ale1800/YULC/3D&Dimensions/yulc_dimensions.png

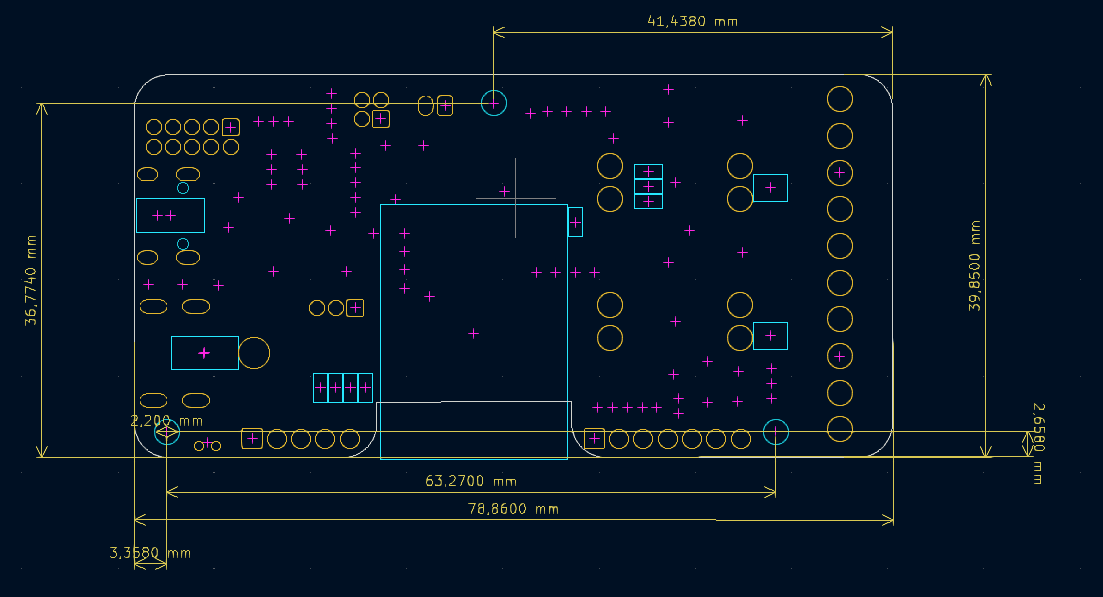
3D&Dimensions/yulc_dimensions.png
