ale1800/YULC/images/enclosure/case-2.jpg

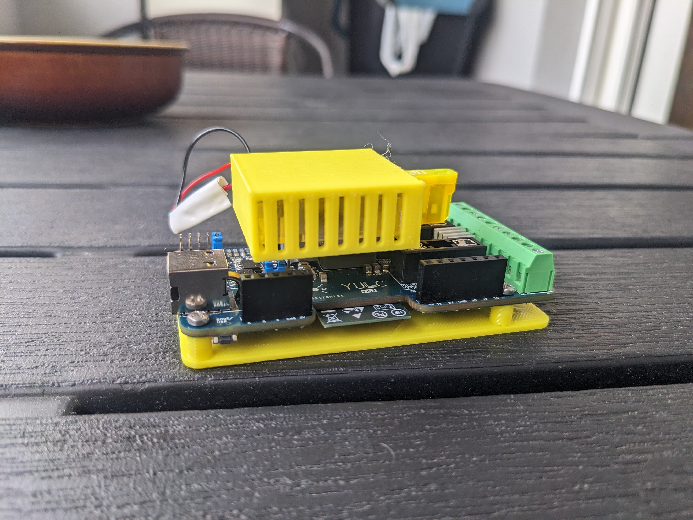
images/enclosure/case-2.jpg
