ale1800/YULC/images/enclosure/case-3.jpg

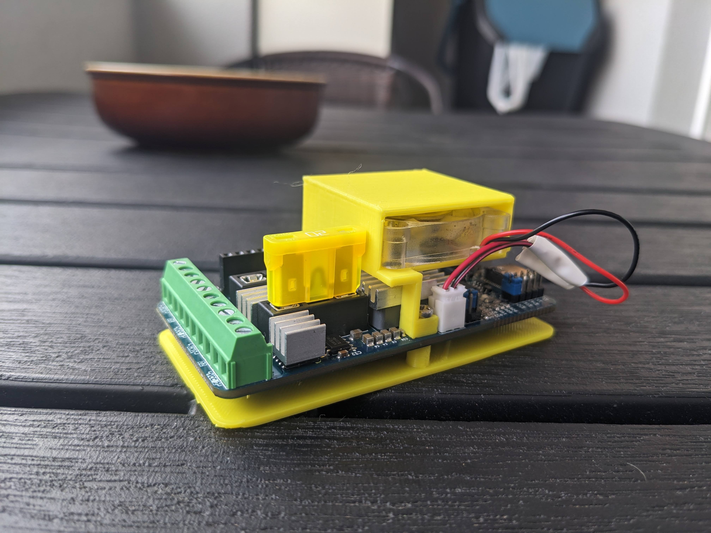
images/enclosure/case-3.jpg
