ale1800/YULC/images/enclosure/case-5.jpg

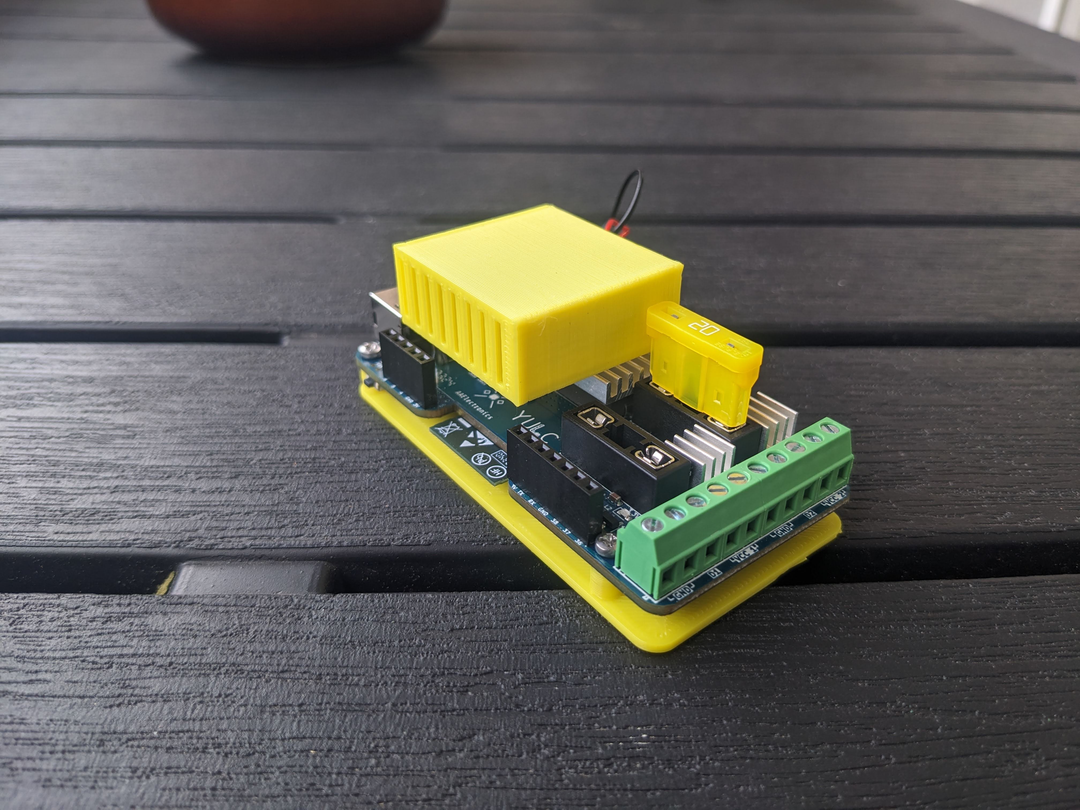
images/enclosure/case-5.jpg
