ale1800/YULC/images/real_use/side.jpg

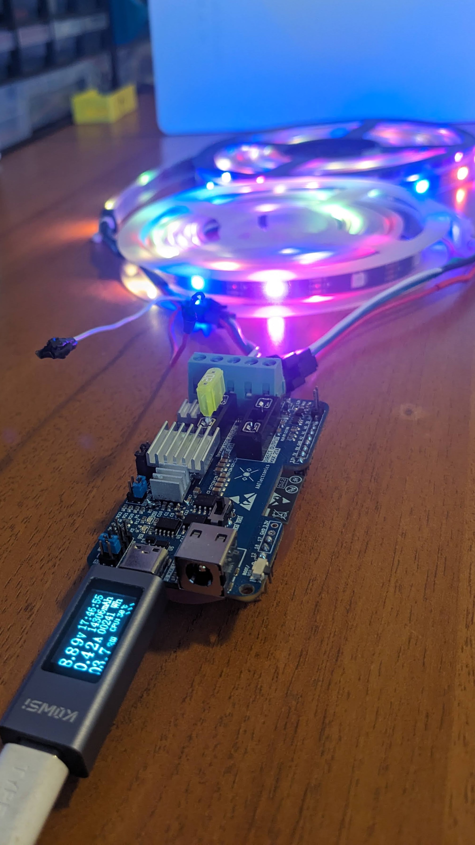
images/real_use/side.jpg
