ale1800/YULC/images/real_use/top_yellow.jpg

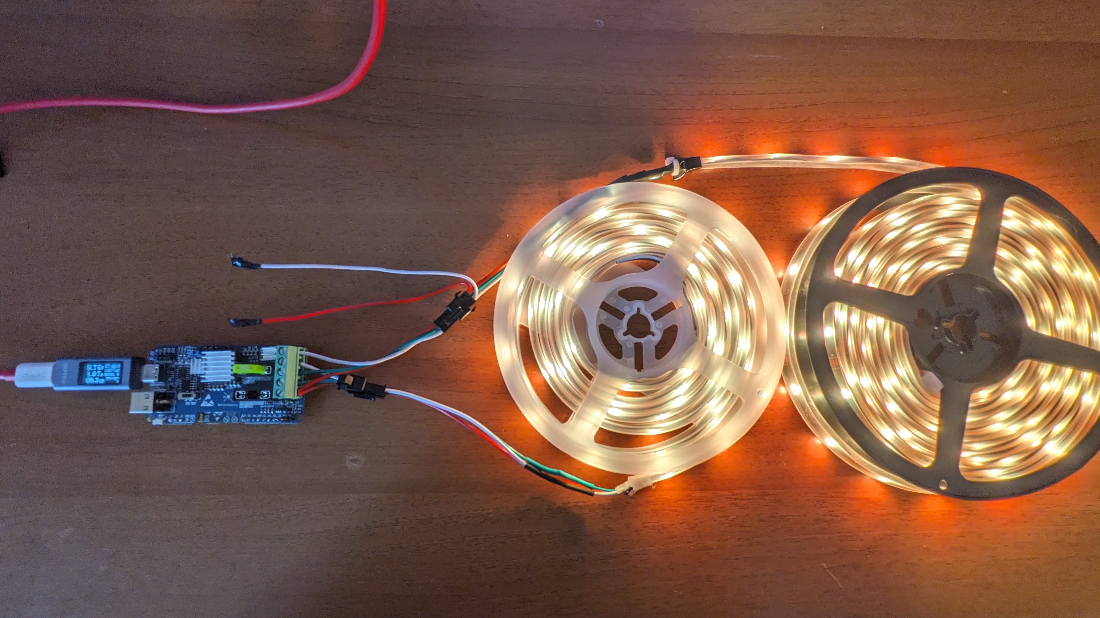
images/real_use/top_yellow.jpg
