ale1800/YULC/images/real_use/top_yulc.jpg

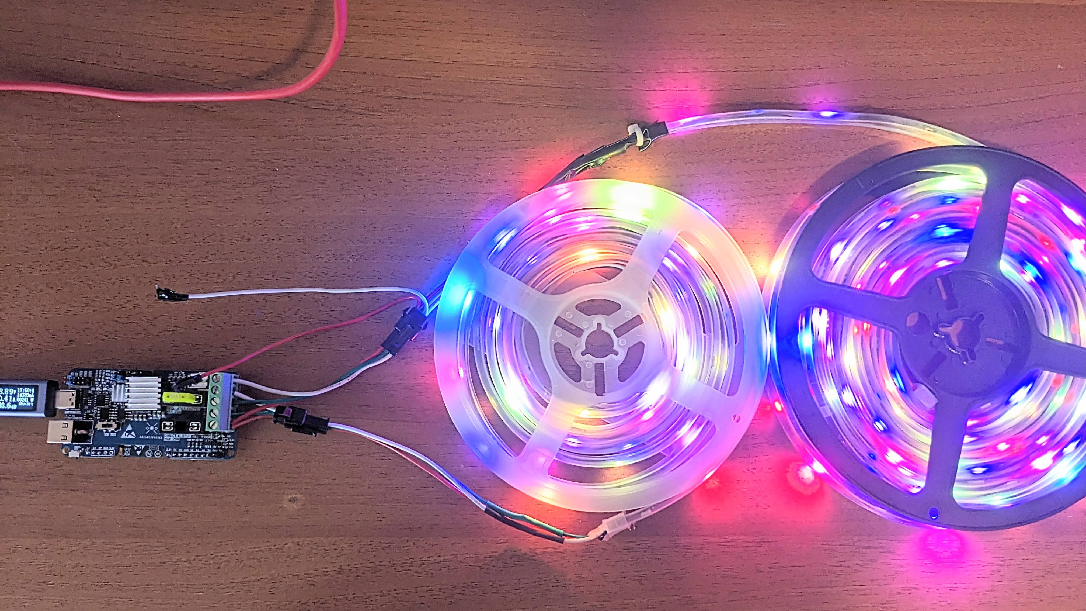
images/real_use/top_yulc.jpg
