ale1800/YULC/images/v2.1/angle-2.jpg

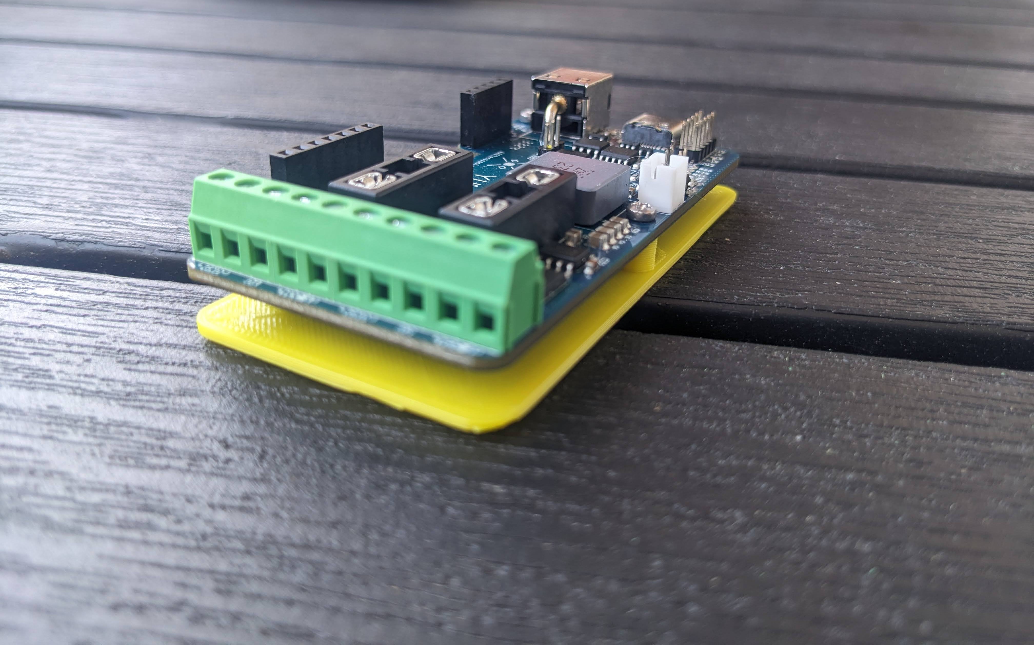
images/v2.1/angle-2.jpg
