ale1800/YULC/images/v2.1/angled.jpg

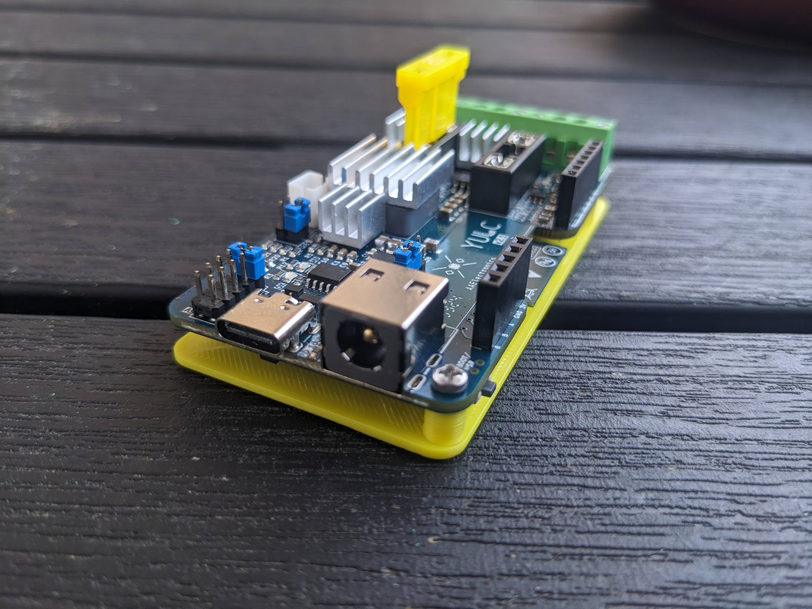
images/v2.1/angled.jpg
