ale1800/YULC/images/v2.1/base_screw.jpg

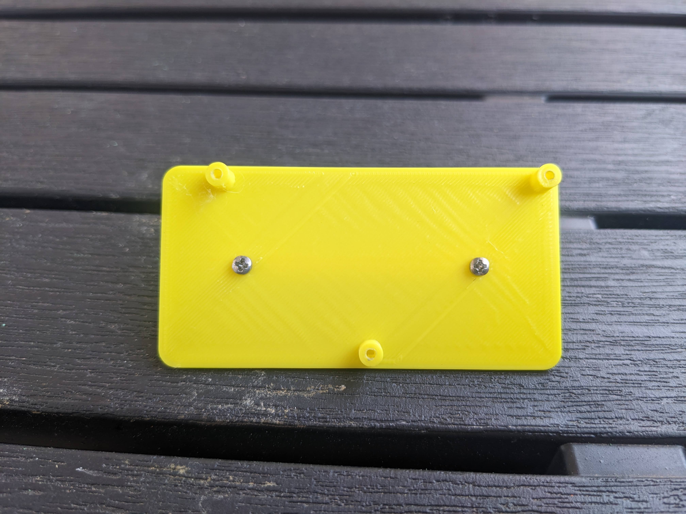
images/v2.1/base_screw.jpg
