ale1800/YULC/images/v2.1/DIN-side.jpg

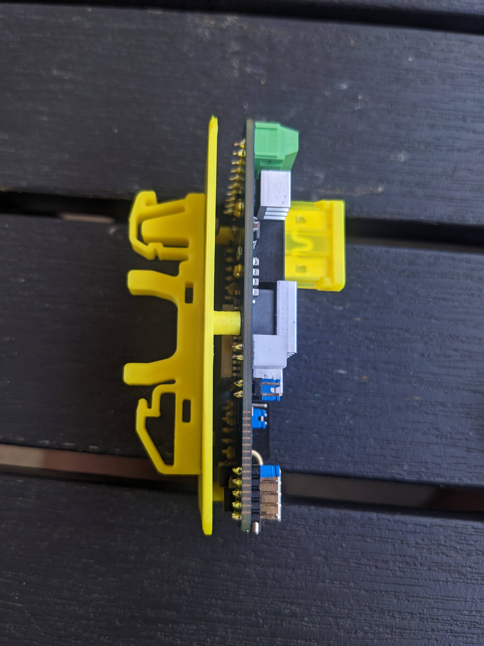
images/v2.1/DIN-side.jpg
