ale1800/YULC/images/v2.1/front_v2.1.jpg

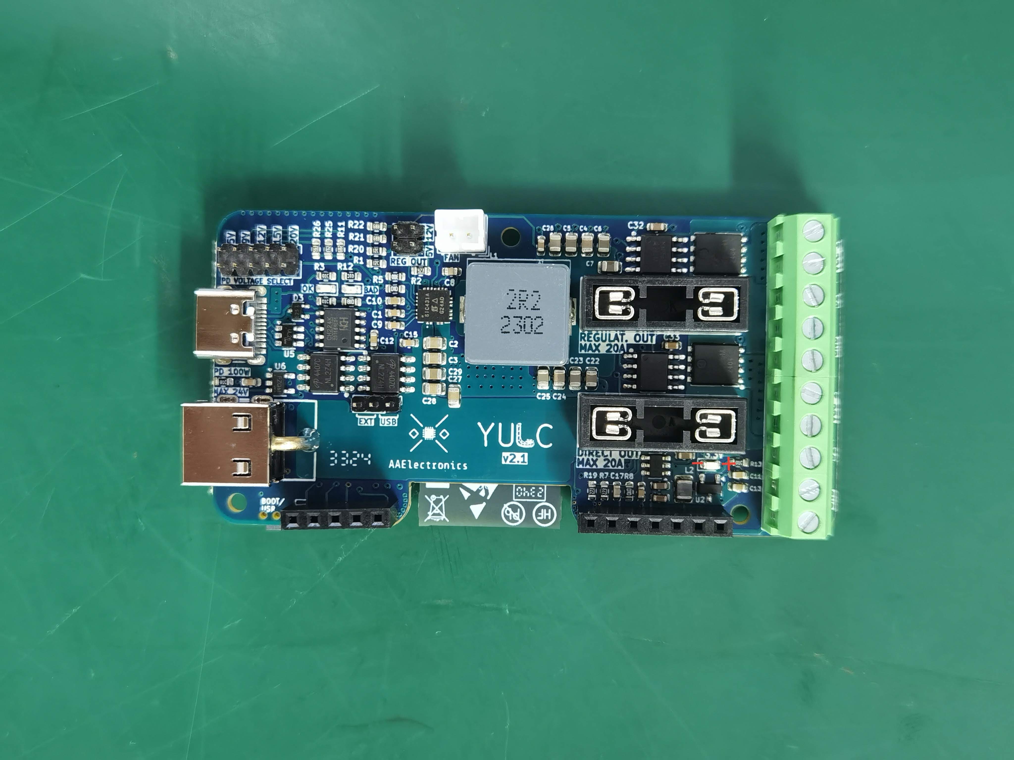
images/v2.1/front_v2.1.jpg
