ale1800/YULC/images/v2.1/side-1.jpg

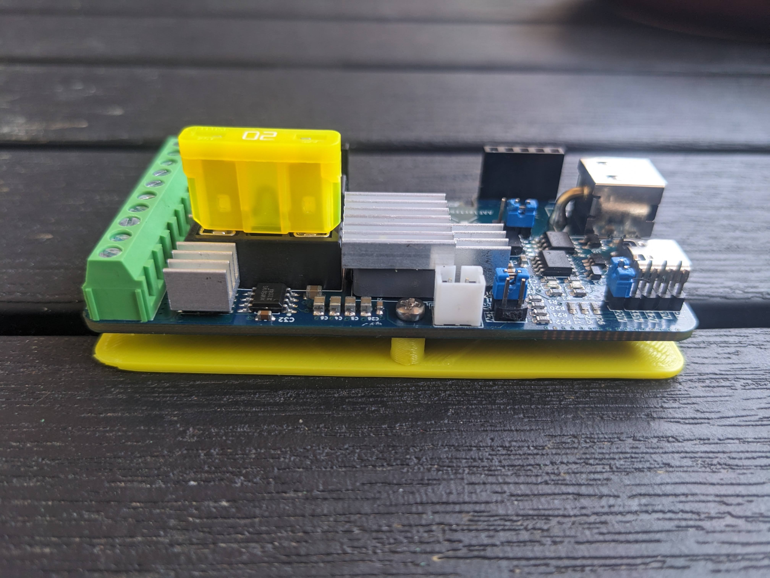
images/v2.1/side-1.jpg
