ale1800/YULC/images/v2.1/side-2.jpg

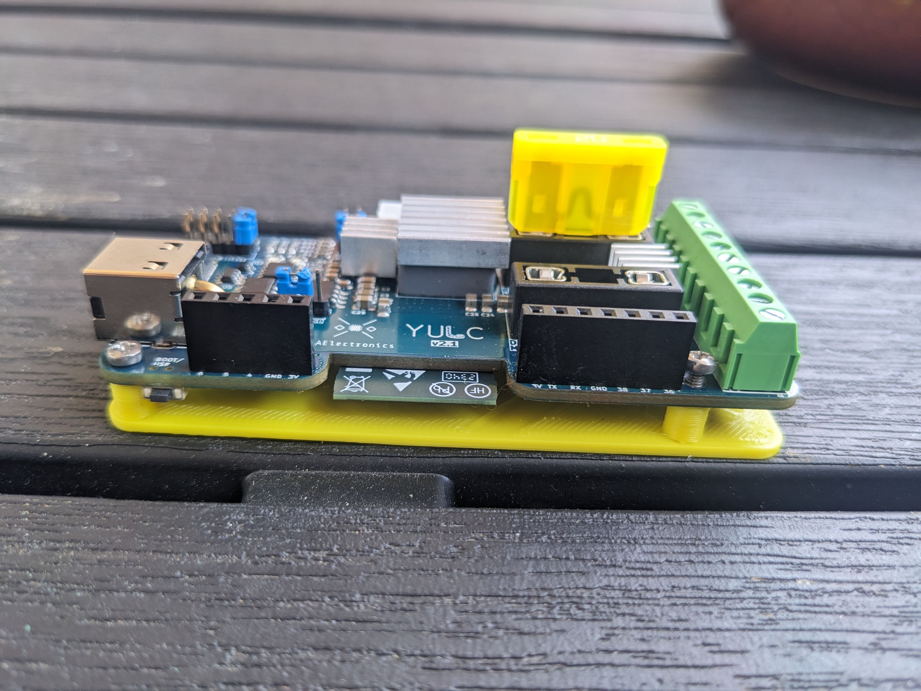
images/v2.1/side-2.jpg
