ale1800/YULC/images/v2.1/side-3.jpg

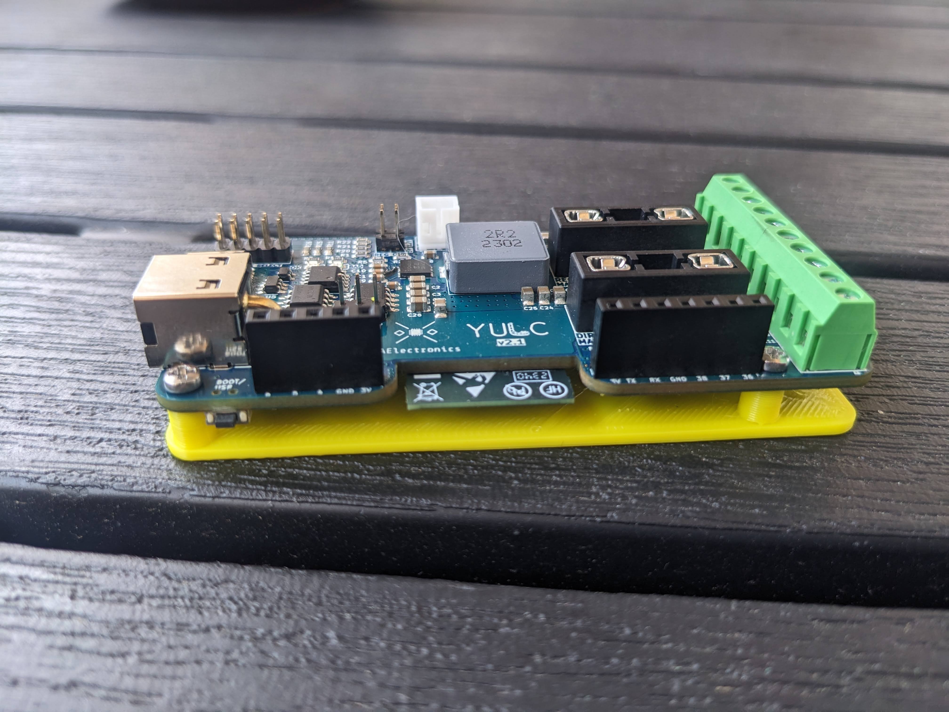
images/v2.1/side-3.jpg
