ale1800/YULC/images/White-bg-images/yulc-angle-02.jpeg

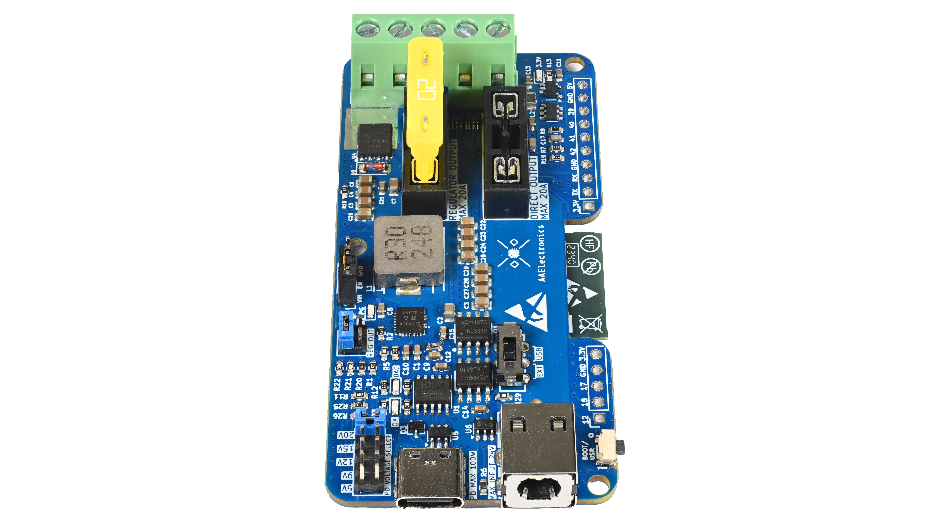
images/White-bg-images/yulc-angle-02.jpeg
