ale1800/YULC/images/White-bg-images/yulc-angle-04.jpeg

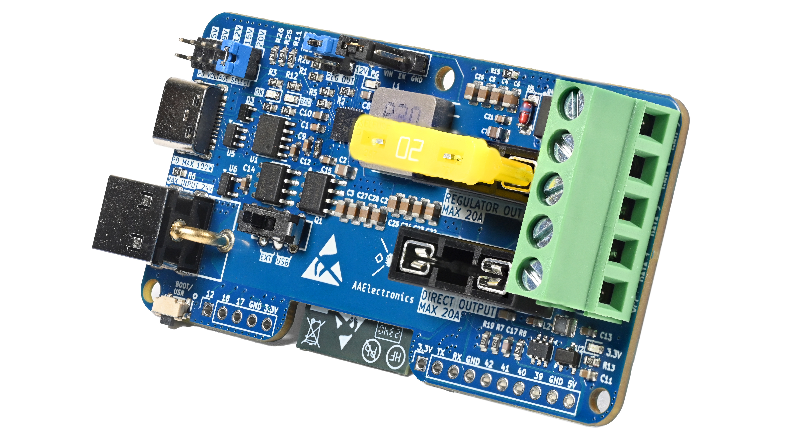
images/White-bg-images/yulc-angle-04.jpeg
