ale1800/YULC/images/White-bg-images/yulc-angle-05.jpeg

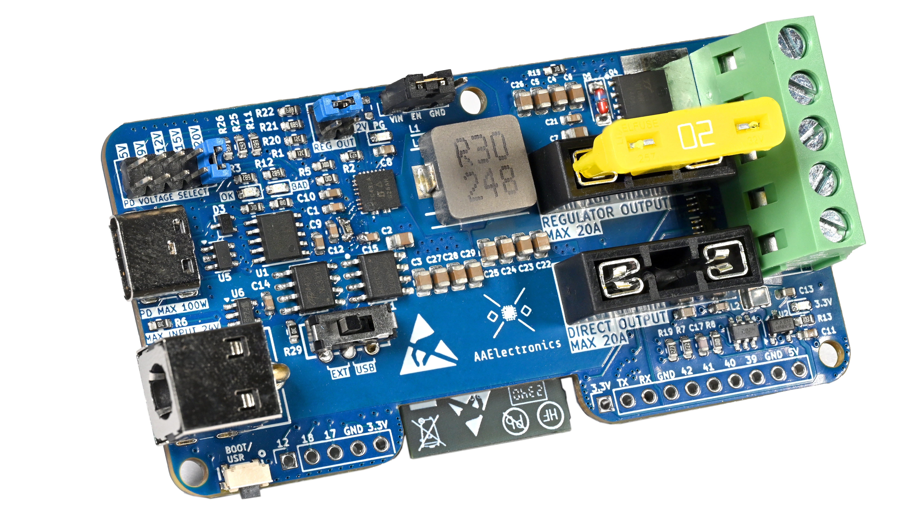
images/White-bg-images/yulc-angle-05.jpeg
