ale1800/YULC/images/White-bg-images/yulc-back-01.jpeg

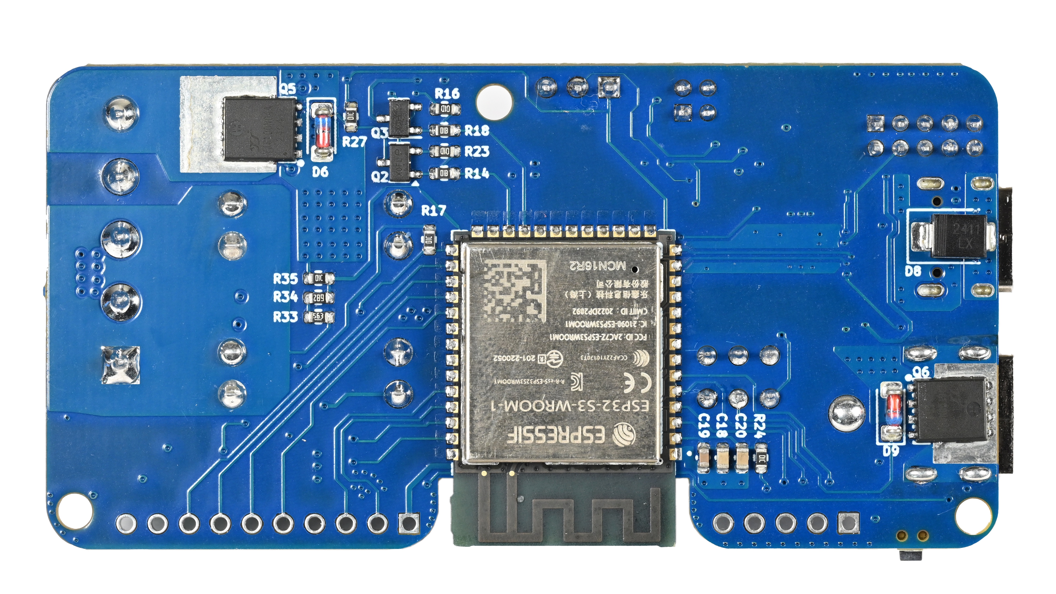
images/White-bg-images/yulc-back-01.jpeg
