ale1800/YULC/images/Wled/HA-yulc.PNG

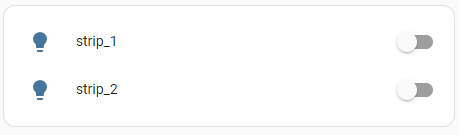
images/Wled/HA-yulc.PNG
